botMaru/water-automation/water_automation_schematic/garage_schematic.kicad_sch

## KiCad design water_automation_schematic/garage_schematic.kicad_sch (2026-05-14)

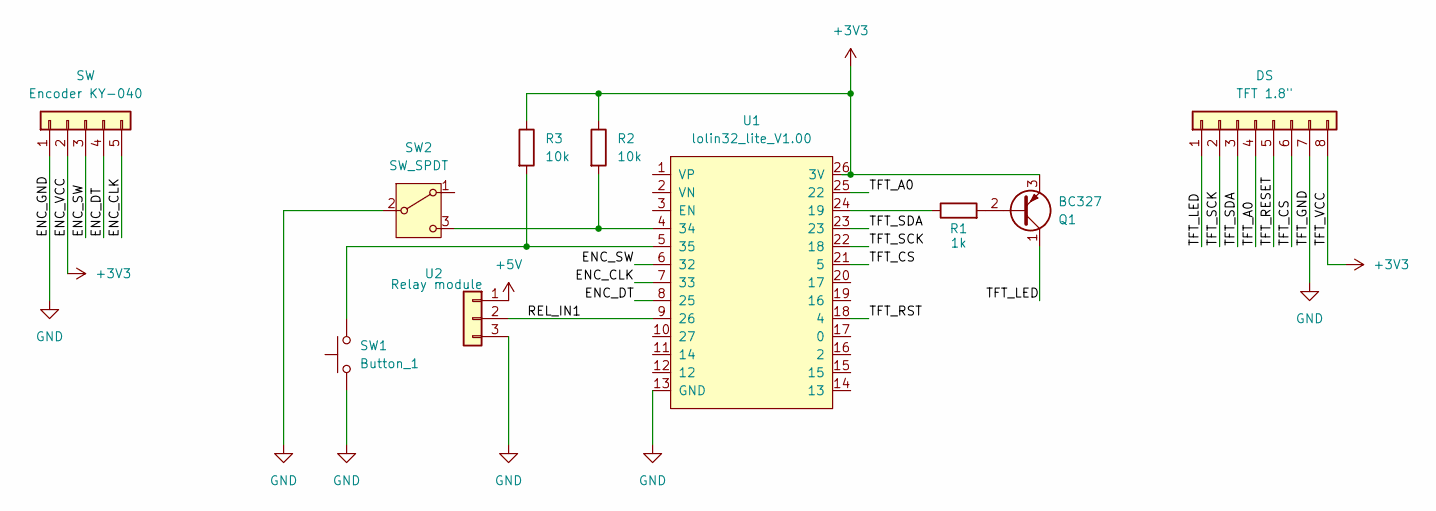
[picture p5: schematic garage_schematic.kicad_sch]

Parts:
DS: TFT 1.8"
Q1: BC327; TO-92_Inline
R1: 1k
R2, R3: 10k
SW: Encoder KY-040
SW1: Button_1
SW2: SW_SPDT
U1: lolin32_lite_V1.00
U2: Relay module

Connections:
+3V3: DS.8, Q1.3 (E), R2.1, R3.1, SW.2, U1.26 (3V)
+5V: U2.1
ENC_CLK: SW.5, U1.7 (33)
ENC_DT: SW.4, U1.8 (25)
ENC_SW: SW.3, U1.6 (32)
GND: DS.7, SW.1, SW1.1, SW2.2 (B), U1.13 (GND), U2.3
unnamed: Q1.2 (B), R1.2
unnamed: R1.1, U1.24 (19)
unnamed: R2.2, SW2.3 (C), U1.4 (34)
unnamed: R3.2, SW1.2, U1.5 (35)
REL_IN1: U1.9 (26), U2.2
TFT_A0: DS.4, U1.25 (22)
TFT_CS: DS.6, U1.21 (5)
TFT_LED: DS.1, Q1.1 (C)
TFT_RESET: DS.5
TFT_RST: U1.18 (4)
TFT_SCK: DS.2, U1.22 (18)
TFT_SDA: DS.3, U1.23
