botMaru/water-automation/water_automation_schematic/power_schematic.kicad_sch

## KiCad design water_automation_schematic/power_schematic.kicad_sch (2026-05-07)

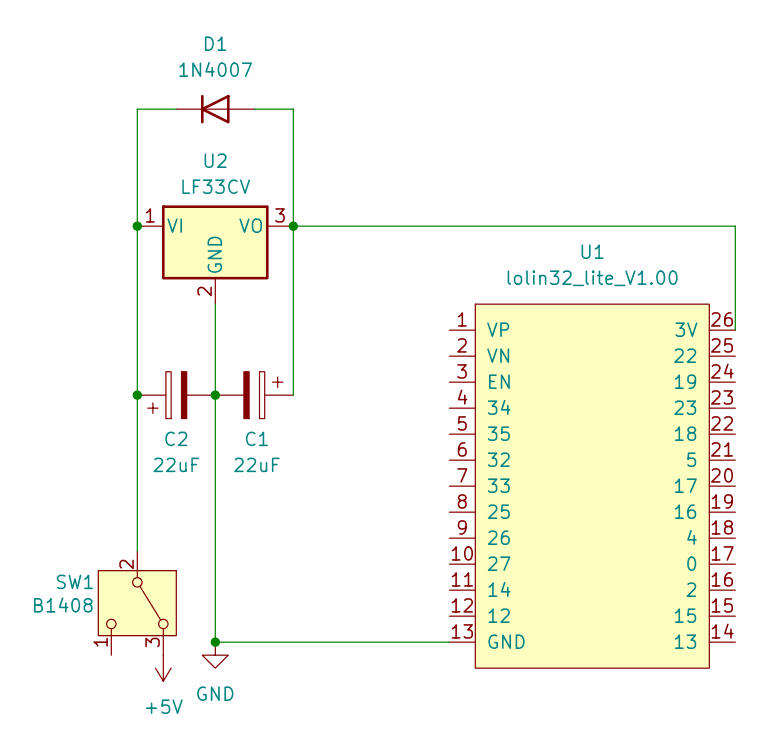
[picture p6: schematic power_schematic.kicad_sch]

Parts:
C1, C2: 22uF
D1: 1N4007; D_SOD-523
SW1: B1408; Nidec_Copal_CAS-120A
U1: lolin32_lite_V1.00
U2: LF33CV; TO-220-3_Vertical

Connections:
+5V: SW1.3 (A)
GND: C1.2, C2.2, U1.13 (GND), U2.2 (GND)
unnamed: C1.1, D1.2 (A), U1.26 (3V), U2.3 (VO)
unnamed: C2.1, D1.1 (K), SW1.2 (B), U2.1 (VI)
