botMaru/water-automation/water_automation_schematic/tank_schematic.kicad_sch

## KiCad design water_automation_schematic/tank_schematic.kicad_sch (2026-06-25)

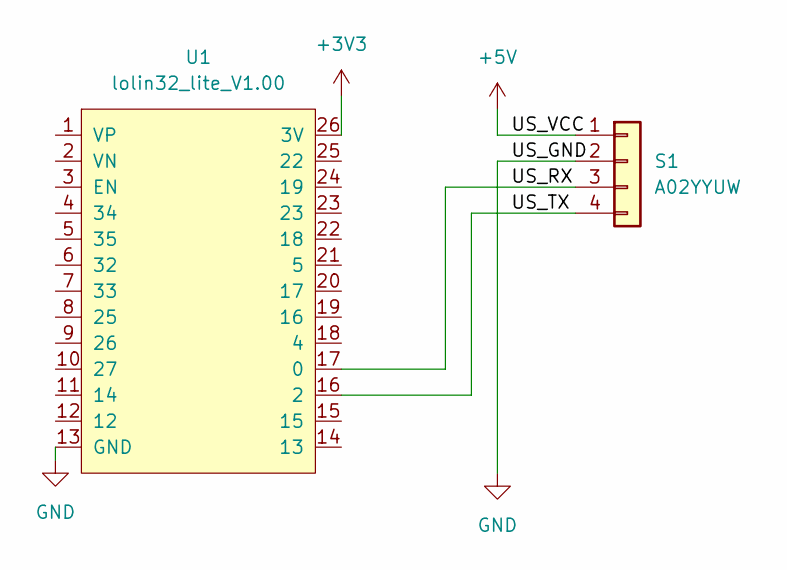
[picture p7: schematic tank_schematic.kicad_sch]

Parts:
S1: A02YYUW
U1: lolin32_lite_V1.00

Connections:
+3V3: U1.26 (3V)
+5V: S1.1
GND: S1.2, U1.13 (GND)
US_RX: S1.3, U1.17 (0)
US_TX: S1.4, U1.16 (2)
