botMaru/water-automation/water_automation_schematic/well_schematic.kicad_sch

## KiCad design water_automation_schematic/well_schematic.kicad_sch (2026-05-07)

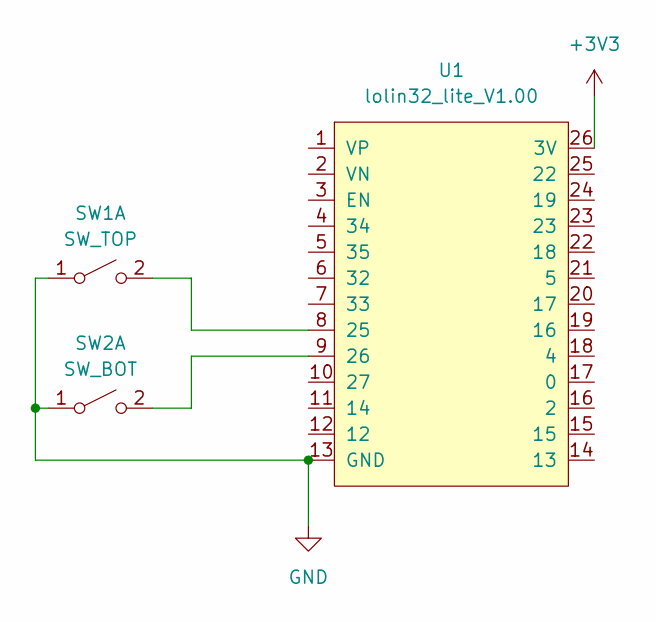
[picture p8: schematic well_schematic.kicad_sch]

Parts:
SW1: SW_TOP
SW2: SW_BOT
U1: lolin32_lite_V1.00

Connections:
+3V3: U1.26 (3V)
GND: SW1.1 (A), SW2.1 (A), U1.13 (GND)
unnamed: SW1.2 (B), U1.8 (25)
unnamed: SW2.2 (B), U1.9 (26)
